Gigahawk/mech423_final_project/mech/programmer_converter_shim/exp_pcb.SLDPRT

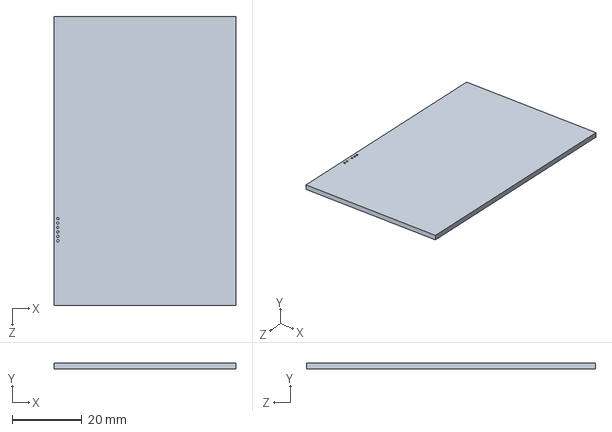
[picture p16: CAD file, 2021-12-13]
mech/programmer_converter_shim/exp_pcb.SLDPRT
52.0 x 1.65 x 82.6 mm
