Gigahawk/mech423_final_project/mech/button_spacer.SLDPRT

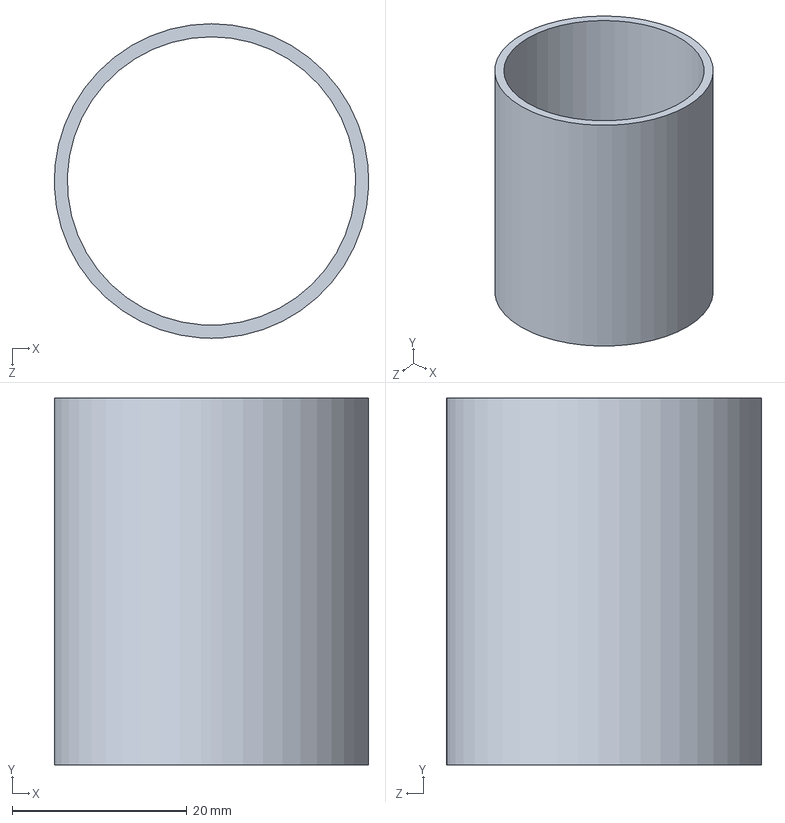
[picture p17: CAD file, 2021-12-24]
mech/button_spacer.SLDPRT
36.0 x 42.0 x 36.0 mm
