Gigahawk/mech423_final_project/mech/strip_collar.SLDPRT

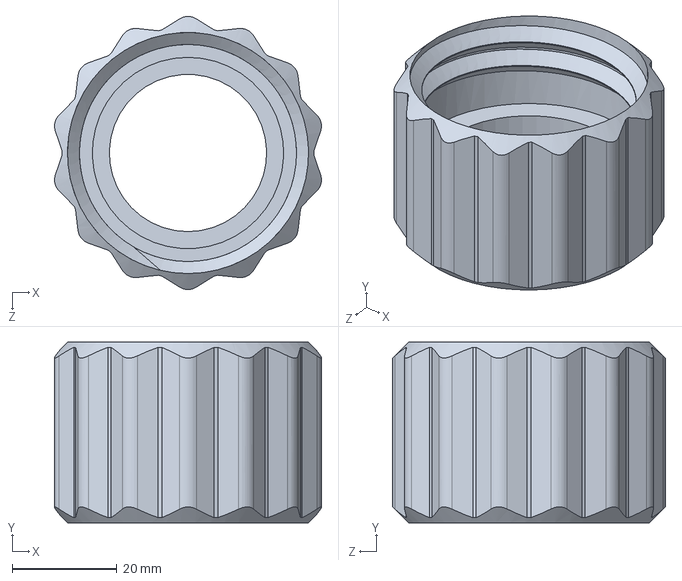
[picture p18: CAD file, 2021-12-24]
mech/strip_collar.SLDPRT
50.9 x 34.5 x 52.1 mm
