Gigahawk/mech423_final_project/mech/button_collar.SLDPRT

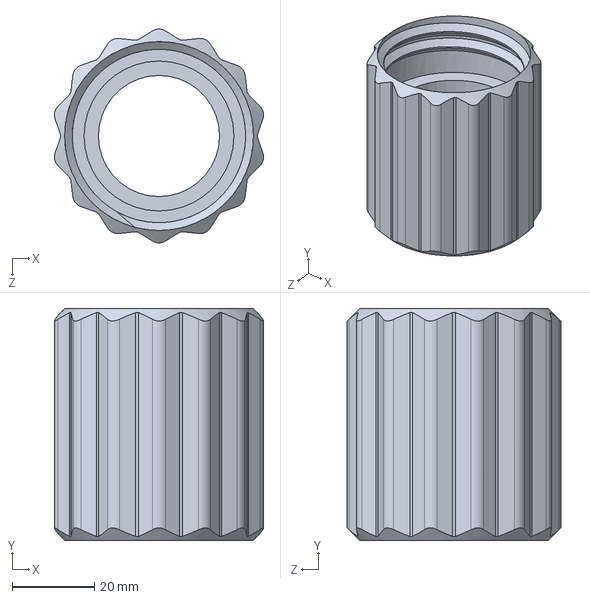
[picture p19: CAD file, 2021-12-24]
mech/button_collar.SLDPRT
50.9 x 56.5 x 52.1 mm
